pola14225/tinycom/tinycom-a13/tinycom-a13-back.png

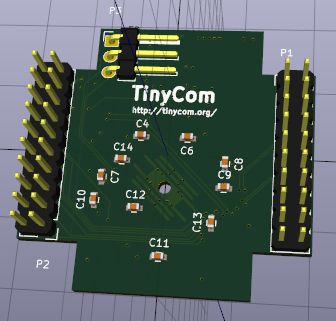
tinycom-a13/tinycom-a13-back.png
