pola14225/tinycom/tinycom-a13/tinycom-a13-board.png

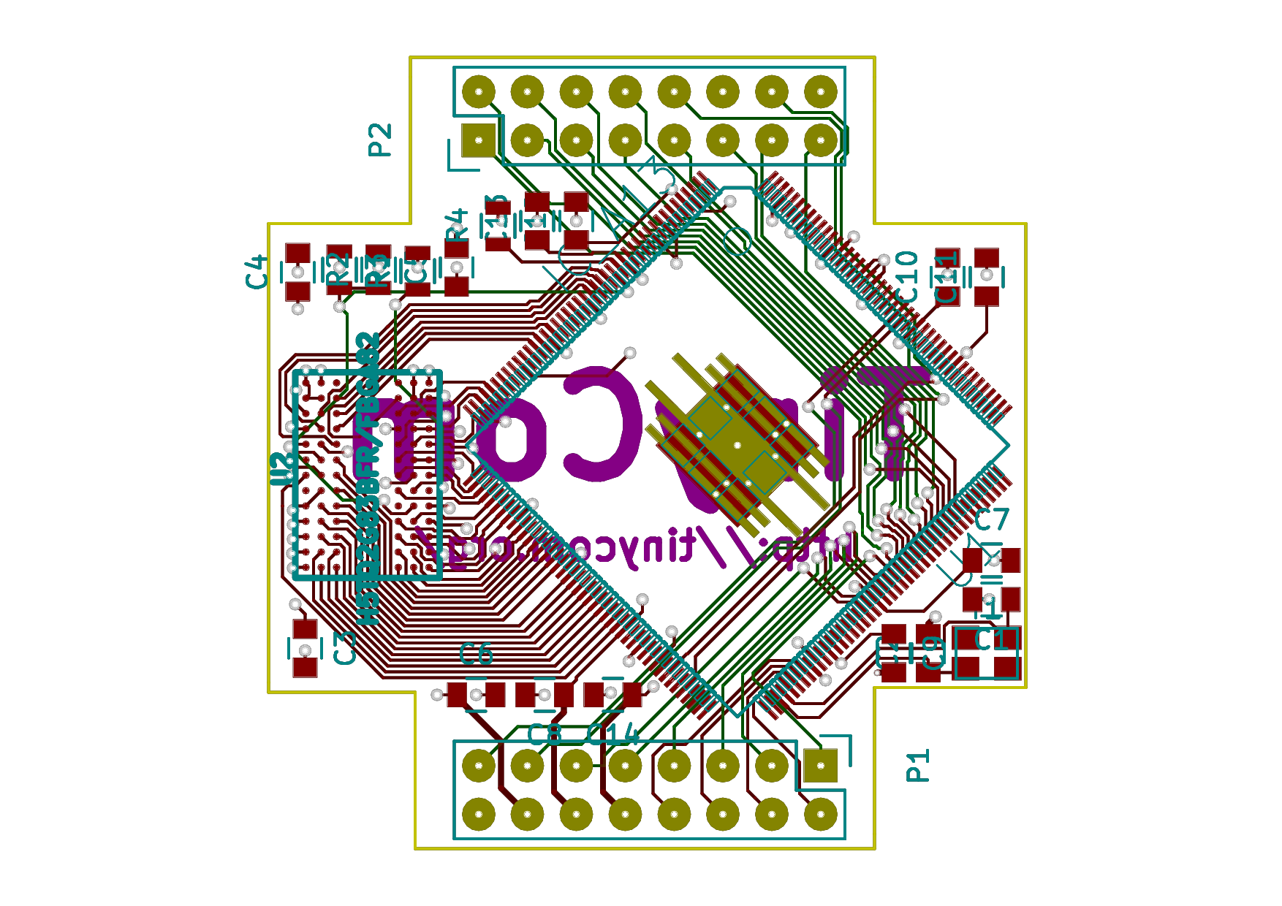
tinycom-a13/tinycom-a13-board.png
