pola14225/tinycom/tinycom-a13/tinycom-a13-front.png

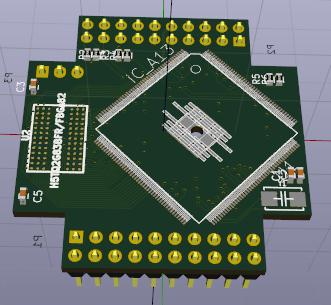
tinycom-a13/tinycom-a13-front.png
