pola14225/tinycom/tinycom-a13/tinycom-a13-layout.png

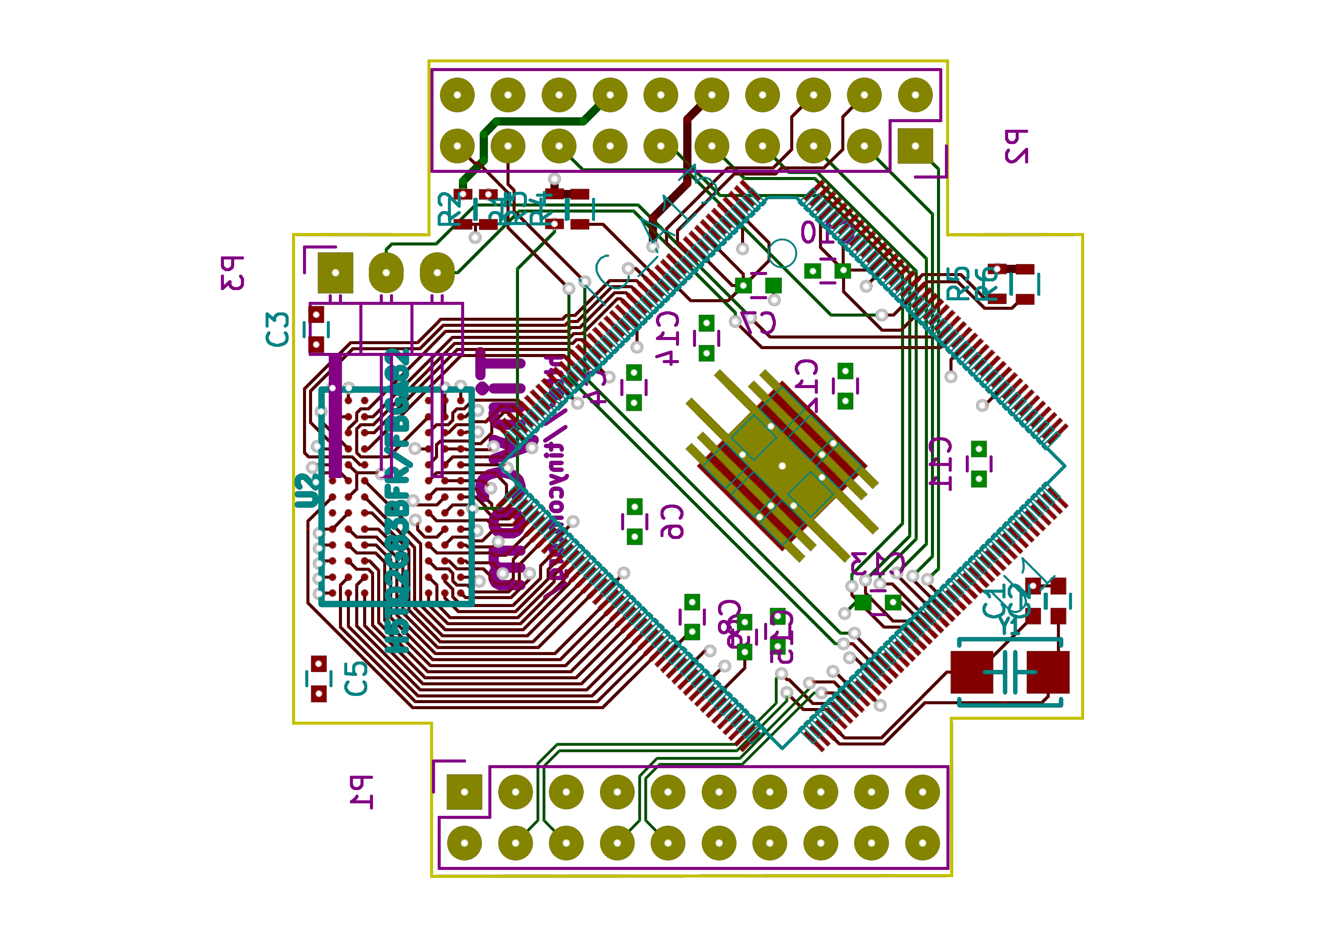
tinycom-a13/tinycom-a13-layout.png
