pola14225/tinycom/tinycom-audio/tinycom-audio-layout.png

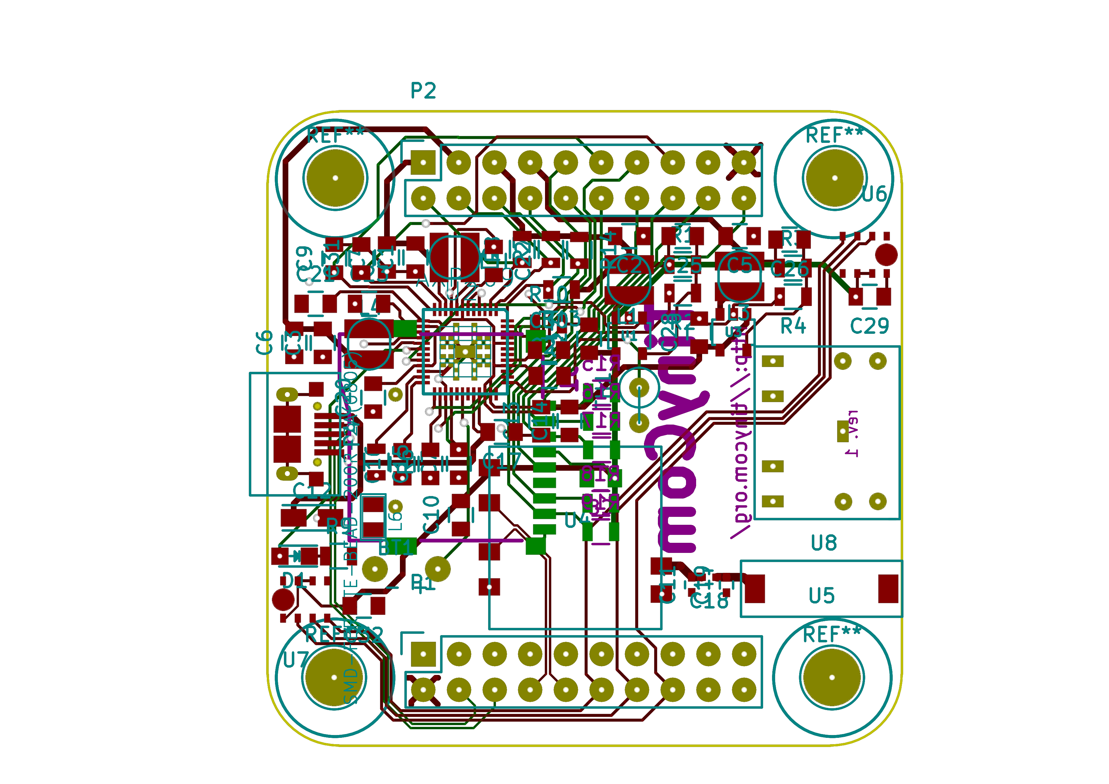
tinycom-audio/tinycom-audio-layout.png
