pola14225/tinycom/tinycom-usb/tinycom-usb-layout.png

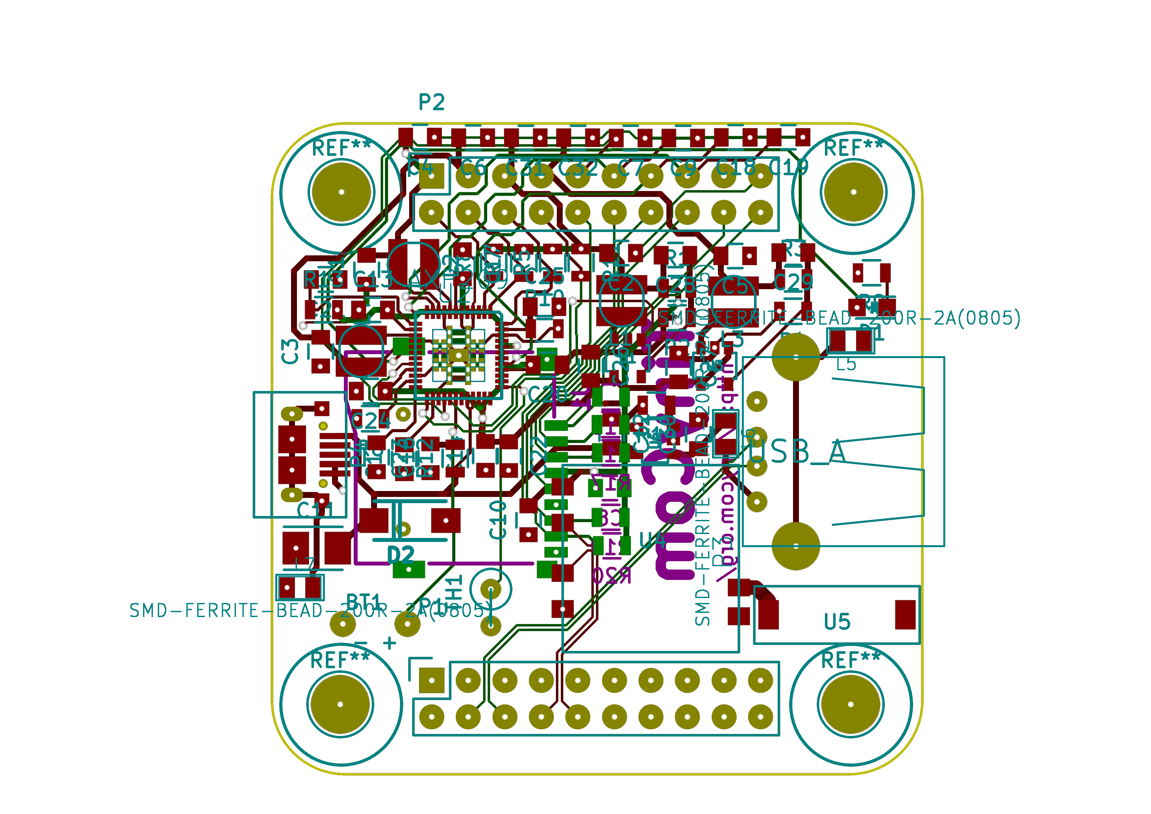
tinycom-usb/tinycom-usb-layout.png
